sonofahutmaker/softshapedisplay/build_files/FOOT_CAP.stl

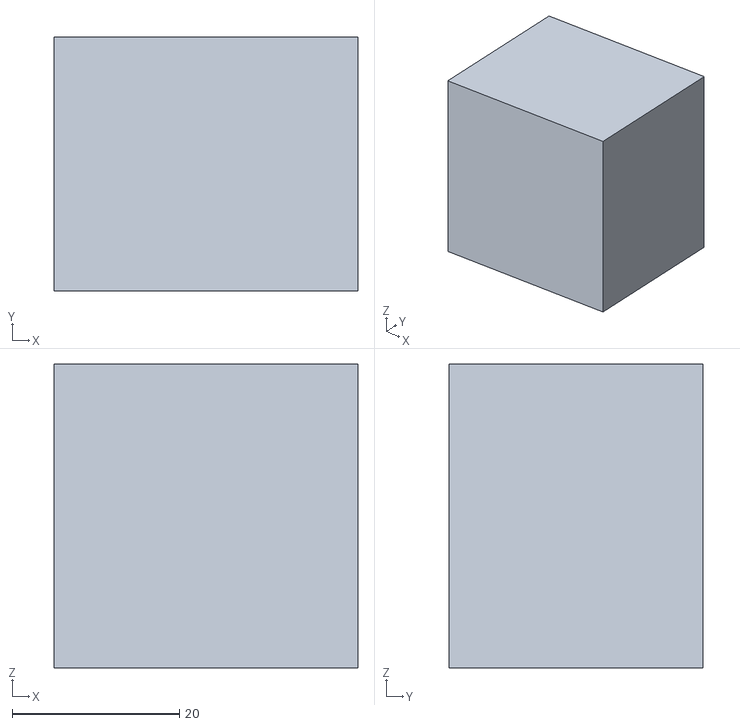
[picture p15: CAD file, 2024-08-22]
build_files/FOOT_CAP.stl
36.4 x 30.4 x 36.4
