sonofahutmaker/softshapedisplay/build_files/CORNER_CAP.stl

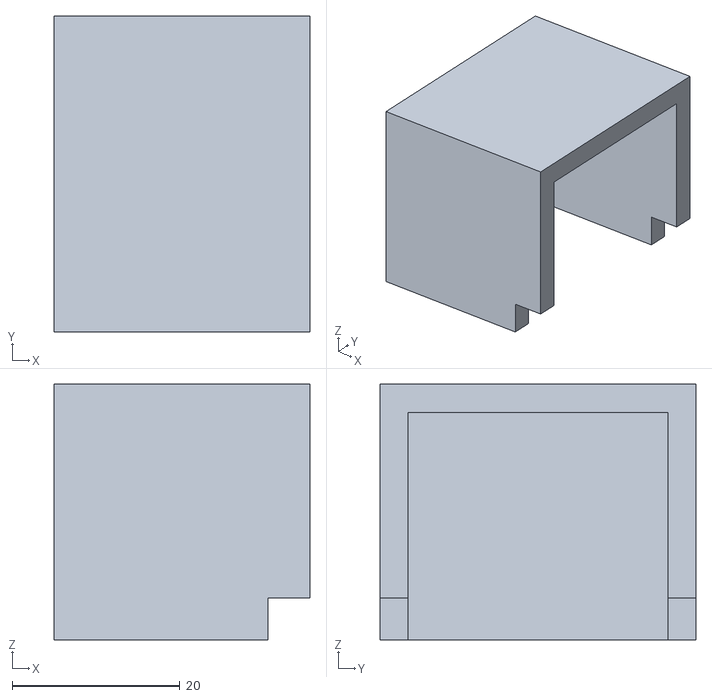
[picture p16: CAD file, 2024-08-22]
build_files/CORNER_CAP.stl
30.5 x 37.7 x 30.5
