sonofahutmaker/softshapedisplay/build_files/STANDARD_SERVO_HOLDER.stl

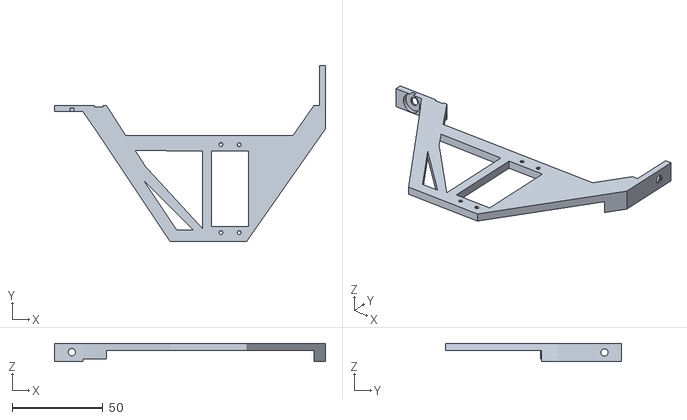
[picture p17: CAD file, 2024-08-22]
build_files/STANDARD_SERVO_HOLDER.stl
149.2 x 96.8 x 10.1
