sonofahutmaker/softshapedisplay/build_files/30INCH_TOP_MOLD_FOR_PRINT/3_1.stl

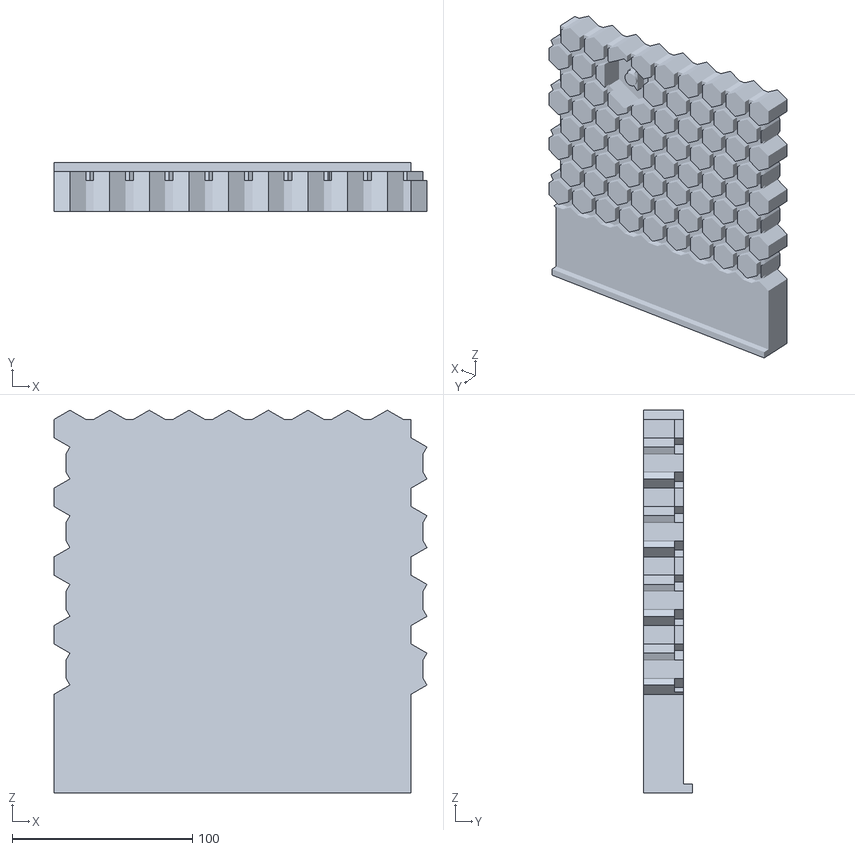
[picture p18: CAD file, 2024-08-22]
build_files/30INCH_TOP_MOLD_FOR_PRINT/3_1.stl
206.8 x 27.2 x 212.1
