sonofahutmaker/softshapedisplay/build_files/30INCH_TOP_MOLD_FOR_PRINT/2_3.stl

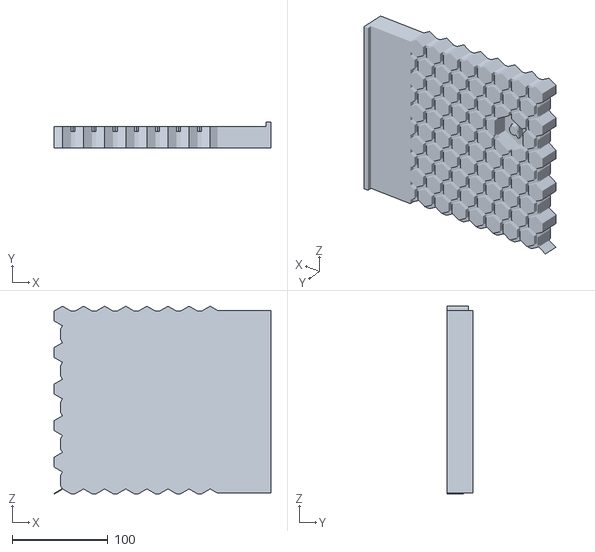
[picture p19: CAD file, 2024-08-22]
build_files/30INCH_TOP_MOLD_FOR_PRINT/2_3.stl
226.2 x 27.3 x 195.6
